MrdUkk/waterfloorheater/firmware/central-unit/MYDS2482.cpp

/*
  DS2482 library for Arduino
  Copyright (C) 2009-2010 Paeae Technologies

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
  You should have readd a copy of the GNU General Public License
  along with this program.  If not, see <http://www.gnu.org/licenses/>.

        crc code is from OneWire library

        -Updates:
                * fixed wireReadByte busyWait (thanks Mike Jackson)
                * Modified search function (thanks Gary Fariss)
                * Fixes errors (c)2020 dUkk

*/
#include "Arduino.h"  // according http://blog.makezine.com/2011/12/01/arduino-1-0-is-out-heres-what-you-need-to-know/

#include "MYDS2482.h"
#include "Wire.h"


#define PTR_STATUS 0xf0
#define PTR_READ 0xe1
#define PTR_CONFIG 0xc3

MYDS2482::MYDS2482(uint8_t addr)
{
        mAddress = 0x18 | addr;
}

//-------helpers
void MYDS2482::begin()
{
        Wire.beginTransmission(mAddress);
}

void MYDS2482::end()
{
        Wire.endTransmission();
}

void MYDS2482::setReadPtr(uint8_t readPtr)
{
        begin();
        Wire.write(0xe1);  // changed from 'send' to 'write' according http://blog.makezine.com/2011/12/01/arduino-1-0-is-out-heres-what-you-need-to-know/'
        Wire.write(readPtr);
        end();
}

uint8_t MYDS2482::readByte()
{
        Wire.requestFrom(mAddress,(uint8_t)1);
        return Wire.read();
}

uint8_t MYDS2482::wireReadStatus(bool setPtr)
{
        if (setPtr)
                setReadPtr(PTR_STATUS);

        return readByte();
}

uint8_t MYDS2482::busyWait(bool setReadPtr)
{
        uint8_t status;
        int loopCount = 1000;
        while((status = wireReadStatus(setReadPtr)) & DS2482_STATUS_BUSY)
        {
                if (--loopCount <= 0)
                {
                        mTimeout = 1;
                        break;
                }
                delayMicroseconds(20);
        }
        return status;
}

//----------interface
uint8_t MYDS2482::reset()
{
        begin();
        Wire.write(0xf0);
        end();

        uint8_t status = busyWait();
        return status & DS2482_STATUS_RST ? true : false;
}

bool MYDS2482::configure(uint8_t config)
{
        busyWait(true);
        begin();
        Wire.write(0xd2);
        Wire.write(config | (~config)<<4);
        end();
        setReadPtr(PTR_CONFIG);

        return readByte() == config;
}

bool MYDS2482::selectChannel(uint8_t channel)
{
        uint8_t ch, ch_read;

        switch (channel)
        {
                case 0:
                default:
                        ch = 0xf0;
                        ch_read = 0xb8;
                        break;
                case 1:
                        ch = 0xe1;
                        ch_read = 0xb1;
                        break;
                case 2:
                        ch = 0xd2;
                        ch_read = 0xaa;
                        break;
                case 3:
                        ch = 0xc3;
                        ch_read = 0xa3;
                        break;
                case 4:
                        ch = 0xb4;
                        ch_read = 0x9c;
                        break;
                case 5:
                        ch = 0xa5;
                        ch_read = 0x95;
                        break;
                case 6:
                        ch = 0x96;
                        ch_read = 0x8e;
                        break;
                case 7:
                        ch = 0x87;
                        ch_read = 0x87;
                        break;
        };

        busyWait(true);
        begin();
        Wire.write(0xc3);
        Wire.write(ch);
        end();
        busyWait();

        uint8_t check = readByte();

        return check == ch_read;
}



bool MYDS2482::wireReset()
{
        busyWait(true);
        begin();
        Wire.write(0xb4);
        end();

        uint8_t status = busyWait();

        return status & DS2482_STATUS_PPD ? true : false;
}


void MYDS2482::wireWriteByte(uint8_t b)
{
        busyWait(true);
        begin();
        Wire.write(0xa5);
        Wire.write(b);
        end();
}

uint8_t MYDS2482::wireReadByte()
{
        busyWait(true);
        begin();
        Wire.write(0x96);
        end();
        busyWait();
        setReadPtr(PTR_READ);
        return readByte();
}

void MYDS2482::wireWriteBit(uint8_t bit)
{
        busyWait(true);
        begin();
        Wire.write(0x87);
        Wire.write(bit ? 0x80 : 0);
        end();
}

uint8_t MYDS2482::wireReadBit()
{
        wireWriteBit(1);
        uint8_t status = busyWait(true);
        return status & DS2482_STATUS_SBR ? 1 : 0;
}

void MYDS2482::wireSkip()
{
        wireWriteByte(0xcc);
}

void MYDS2482::wireSelect(const uint8_t rom[8])
{
        wireWriteByte(0x55);
        for (int i=0;i<8;i++)
                wireWriteByte(rom[i]);
}


#if ONEWIRE_SEARCH
void MYDS2482::wireResetSearch()
{
        searchExhausted = 0;
        searchLastDisrepancy = 0;

        for(uint8_t i = 0; i<8; i++)
                searchAddress[i] = 0;
}

uint8_t MYDS2482::wireSearch(uint8_t *newAddr)
{
        uint8_t i;
        uint8_t direction;
        uint8_t last_zero=0;

        if (searchExhausted)
                return 0;

        if (!wireReset())
                return 0;

        busyWait(true);
        wireWriteByte(0xf0);

        for(i=1;i<65;i++)
        {
                int romByte = (i-1)>>3;
                int romBit = 1<<((i-1)&7);

                if (i < searchLastDisrepancy)
                        direction = searchAddress[romByte] & romBit;
                else
                        direction = i == searchLastDisrepancy;

                busyWait();
                begin();
                Wire.write(0x78);
                Wire.write(direction ? 0x80 : 0);
                end();
                uint8_t status = busyWait();

                uint8_t id = status & DS2482_STATUS_SBR;
                uint8_t comp_id = status & DS2482_STATUS_TSB;
                direction = status & DS2482_STATUS_DIR;

                if (id && comp_id)
                        return 0;
                else
                {
                        if (!id && !comp_id && !direction)
                                last_zero = i;
                }

                if (direction)
                        searchAddress[romByte] |= romBit;
                else
                        searchAddress[romByte] &= (uint8_t)~romBit;
        }

        searchLastDisrepancy = last_zero;

        if (last_zero == 0)
                searchExhausted = 1;

        for (i=0;i<8;i++)
                newAddr[i] = searchAddress[i];

        return 1;
}
#endif

uint8_t MYDS2482::devicesCount(bool printAddress){
  uint8_t address[8];
  uint8_t count = 0;
  String SerialNumber = "";

  wireResetSearch();
  while (wireSearch(address)){
    count++;
        SerialNumber = "";
    for (uint8_t i = 0; i < 8; i++){
      if (address[i] < 0x10) SerialNumber += "0";
      SerialNumber += String(address[i], HEX);
      if (i < 7) SerialNumber += "-";
    }
    if (printAddress){
      Serial.print(SerialNumber);
         deviceName(address[0]);
         Serial.println();
    }
  }
  return count;
}

#if ONEWIRE_CRC
// The 1-Wire CRC scheme is described in Maxim Application Note 27:
// "Understanding and Using Cyclic Redundancy Checks with Maxim iButton Products"
//

uint8_t MYDS2482::crc8(const uint8_t *addr, uint8_t len)
{
        uint8_t crc=0;

        for (uint8_t i=0; i<len;i++)
        {
                uint8_t inbyte = addr[i];
                for (uint8_t j=0;j<8;j++)
                {
                        uint8_t mix = (crc ^ inbyte) & 0x01;
                        crc >>= 1;
                        if (mix)
                                crc ^= 0x8C;

                        inbyte >>= 1;
                }
        }
        return crc;
}

#endif
